V4LL1/vaccine-transport-iot/diagrams/camada analise.png

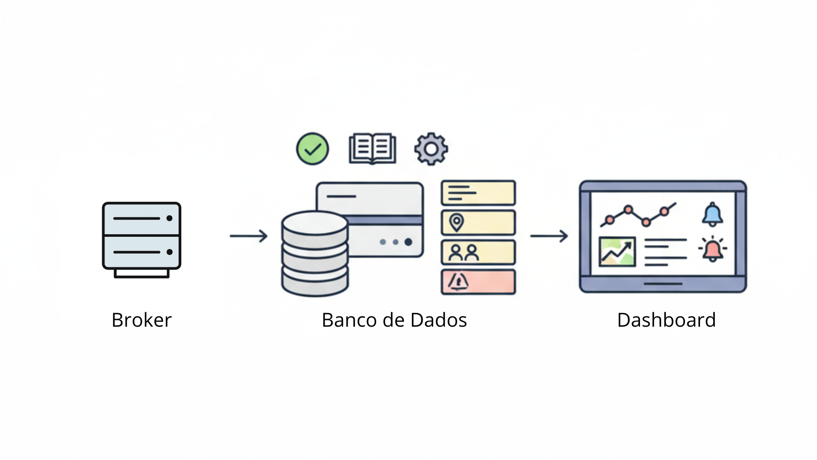
diagrams/camada analise.png
