V4LL1/vaccine-transport-iot/diagrams/camada de analise.png

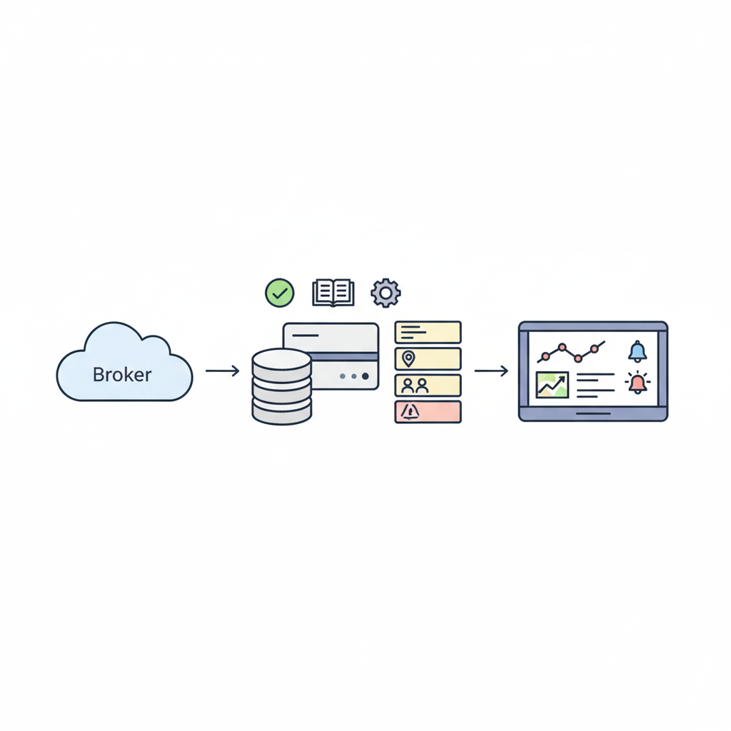
diagrams/camada de analise.png
