V4LL1/vaccine-transport-iot/diagrams/camada de ação.png

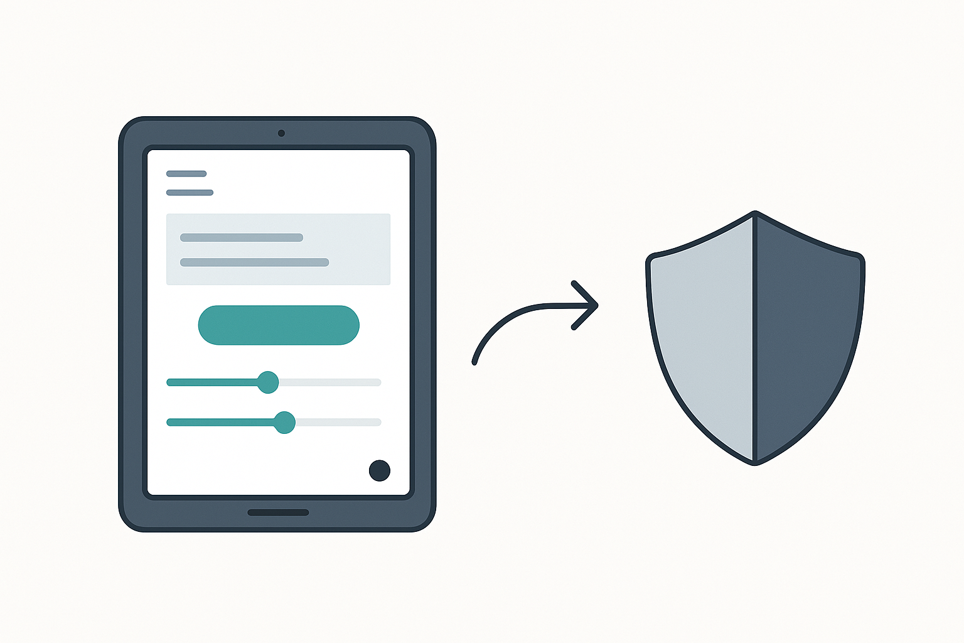
diagrams/camada de ação.png
