V4LL1/vaccine-transport-iot/diagrams/Camada de percepção (1).png

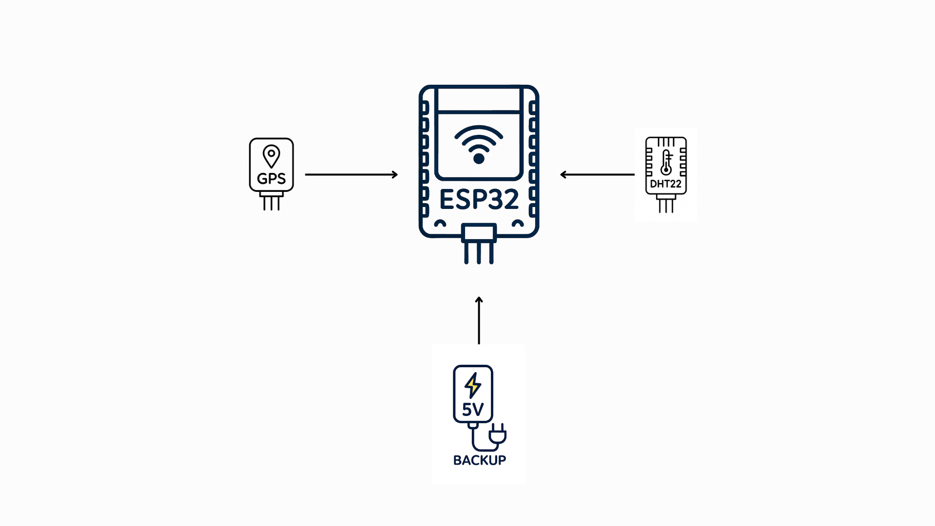
diagrams/Camada de percepção (1).png
