V4LL1/vaccine-transport-iot/diagrams/caminha com vacina.png

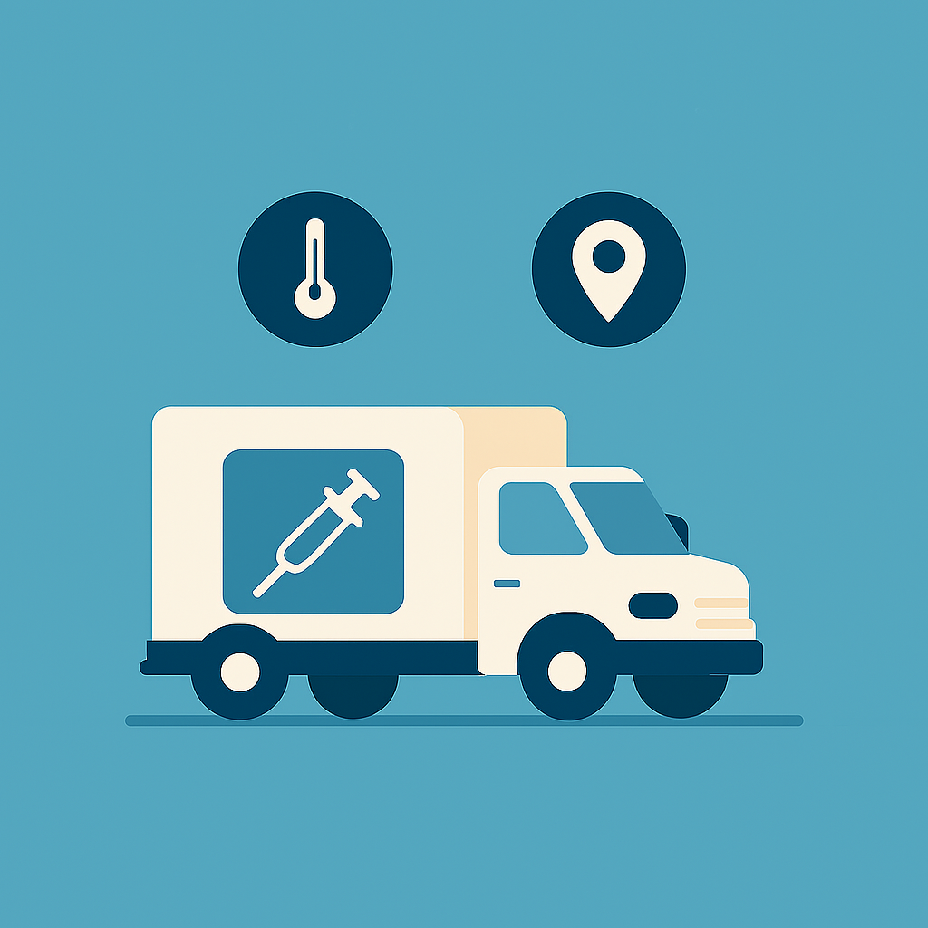
diagrams/caminha com vacina.png
