V4LL1/vaccine-transport-iot/diagrams/caminhao com vacina & hacker.png

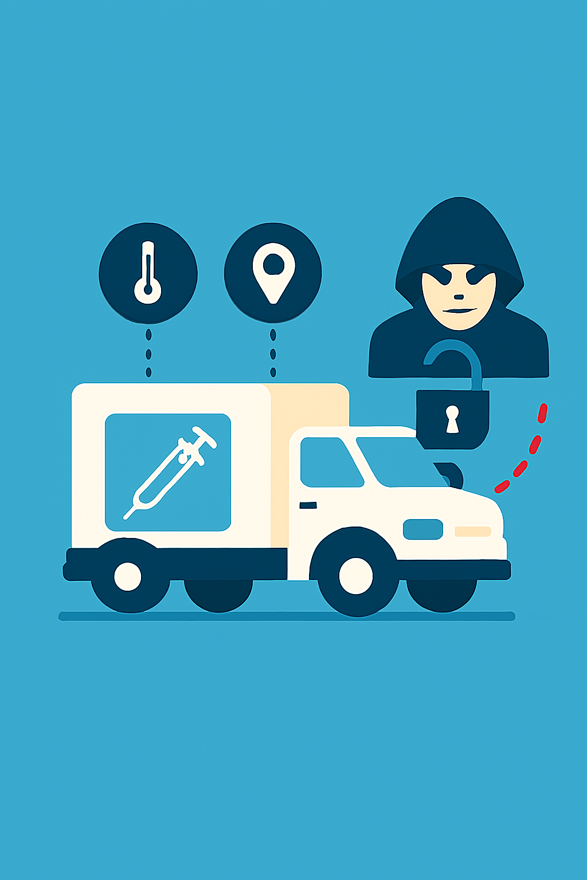
diagrams/caminhao com vacina & hacker.png
