V4LL1/vaccine-transport-iot/diagrams/database.png

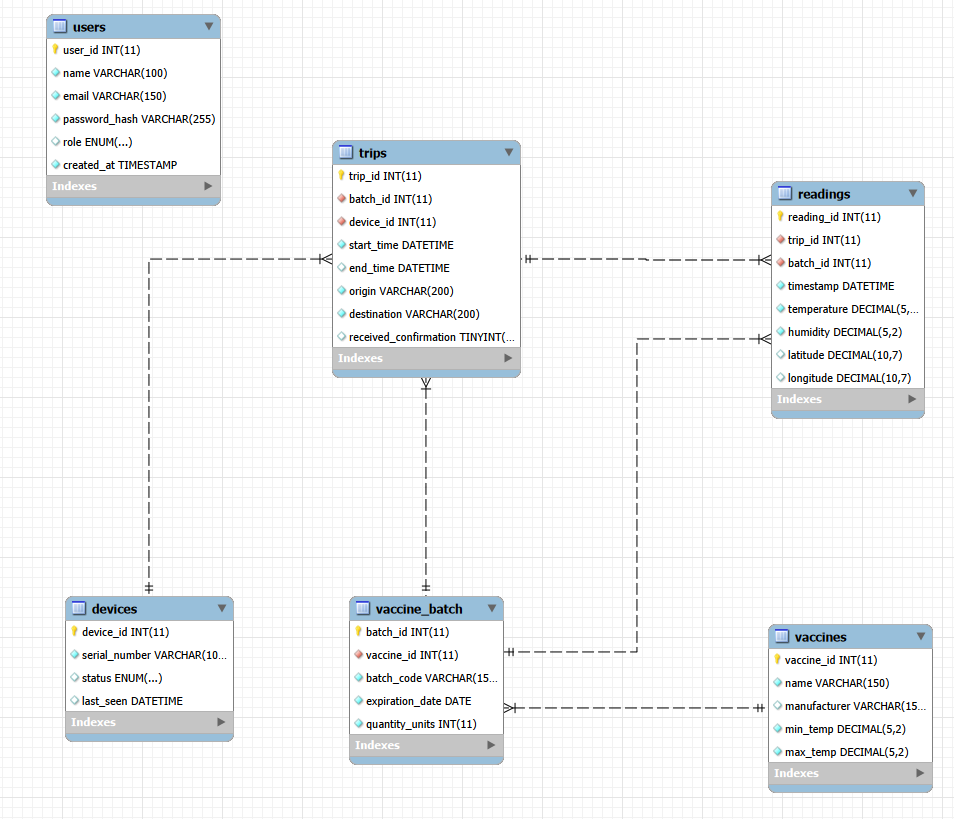
diagrams/database.png
