V4LL1/vaccine-transport-iot/diagrams/diagrama simples.png

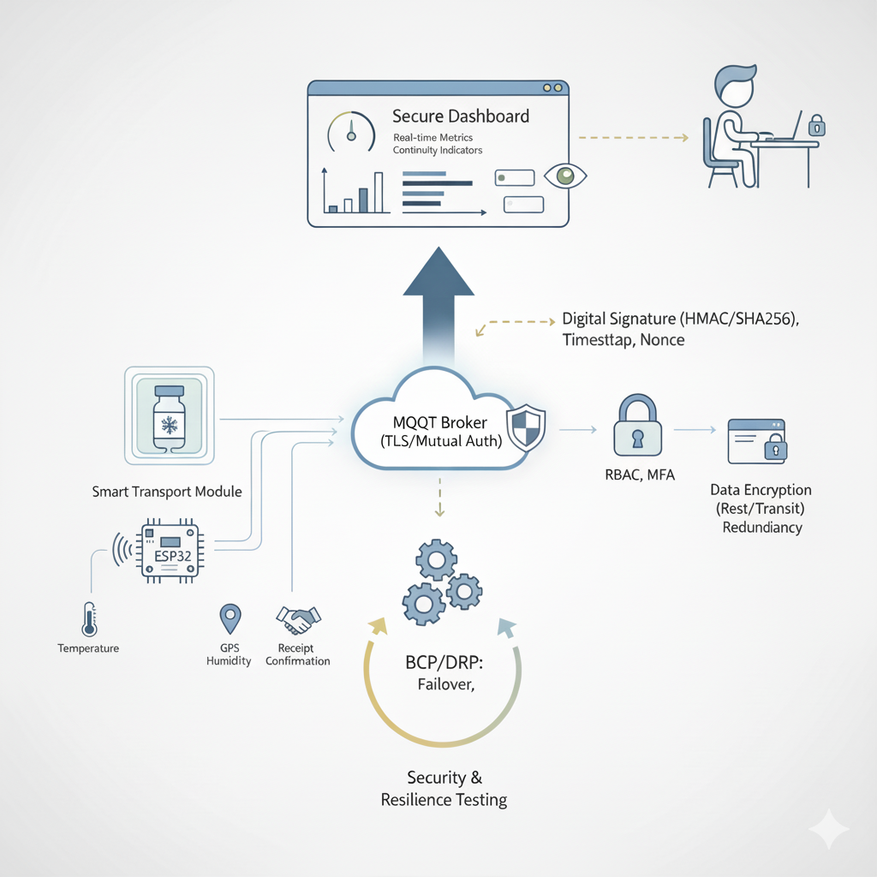
diagrams/diagrama simples.png
