V4LL1/vaccine-transport-iot/diagrams/ER.png

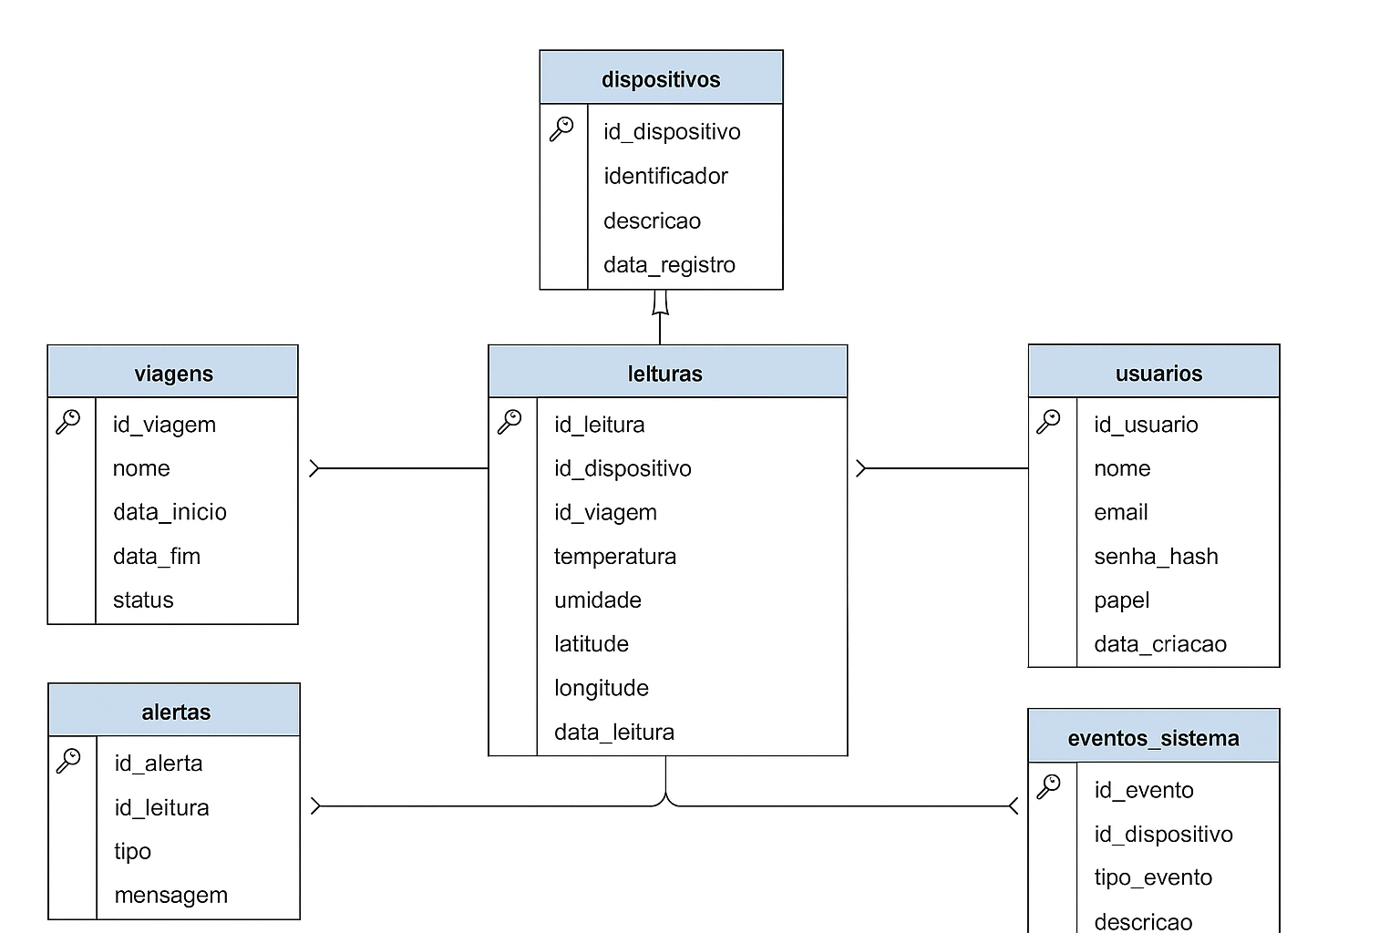
diagrams/ER.png
