V4LL1/vaccine-transport-iot/diagrams/Fases da metodologia.png

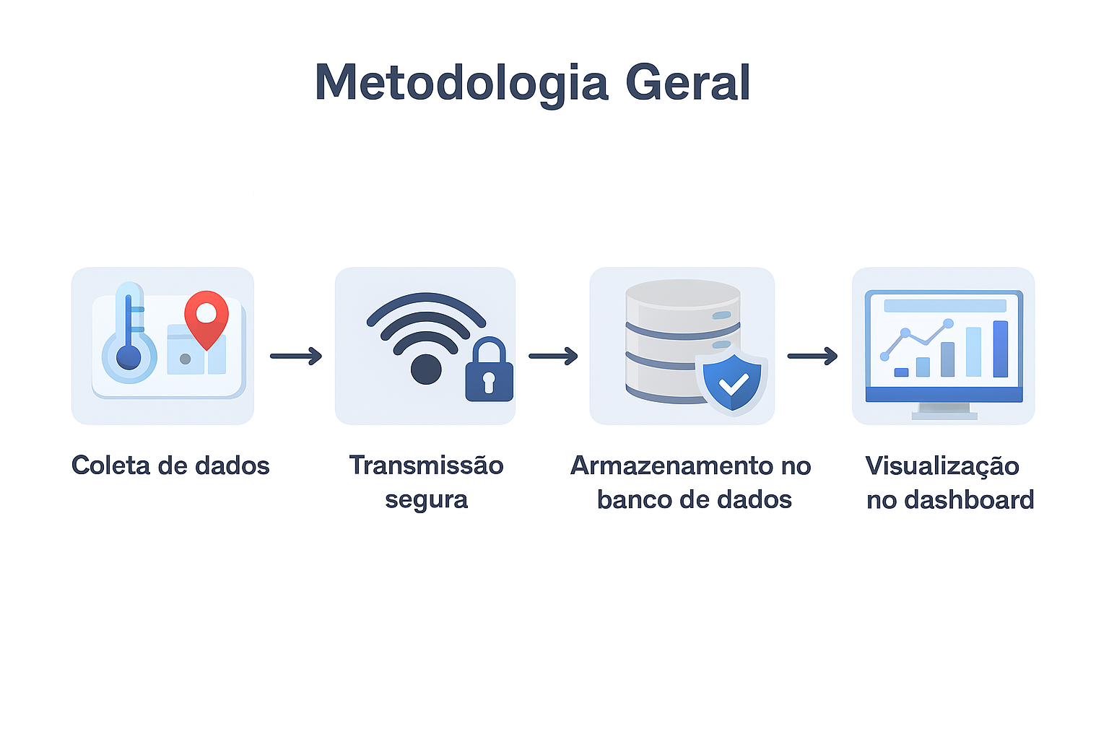
diagrams/Fases da metodologia.png
