V4LL1/vaccine-transport-iot/diagrams/individual modules/banco de dados.png

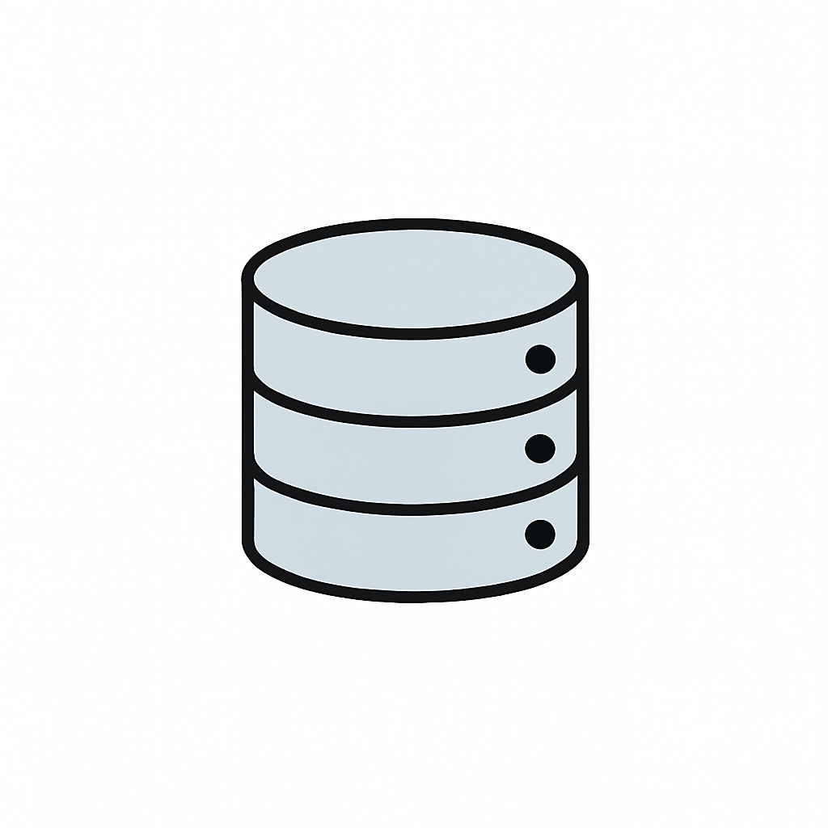
diagrams/individual modules/banco de dados.png
