V4LL1/vaccine-transport-iot/diagrams/individual modules/broker mqtt.png

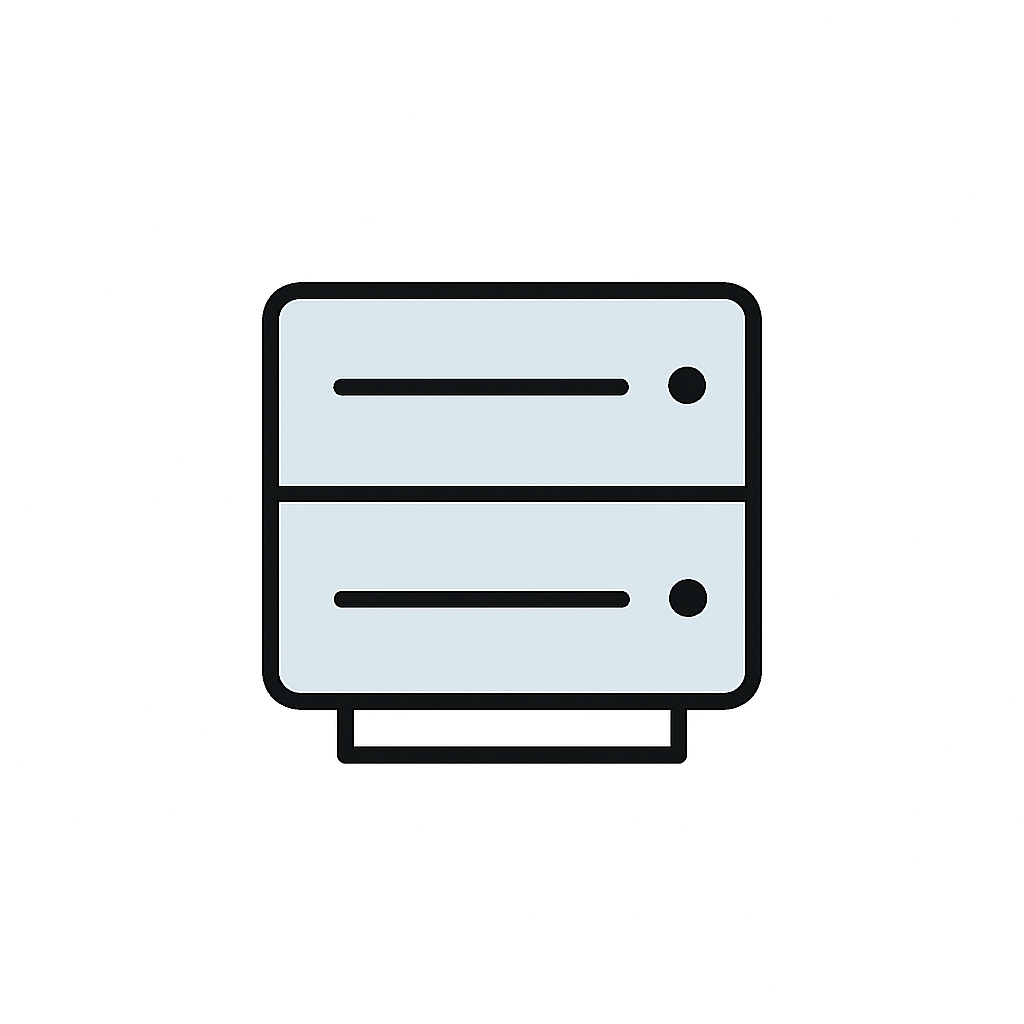
diagrams/individual modules/broker mqtt.png
