V4LL1/vaccine-transport-iot/diagrams/individual modules/cadeado.png

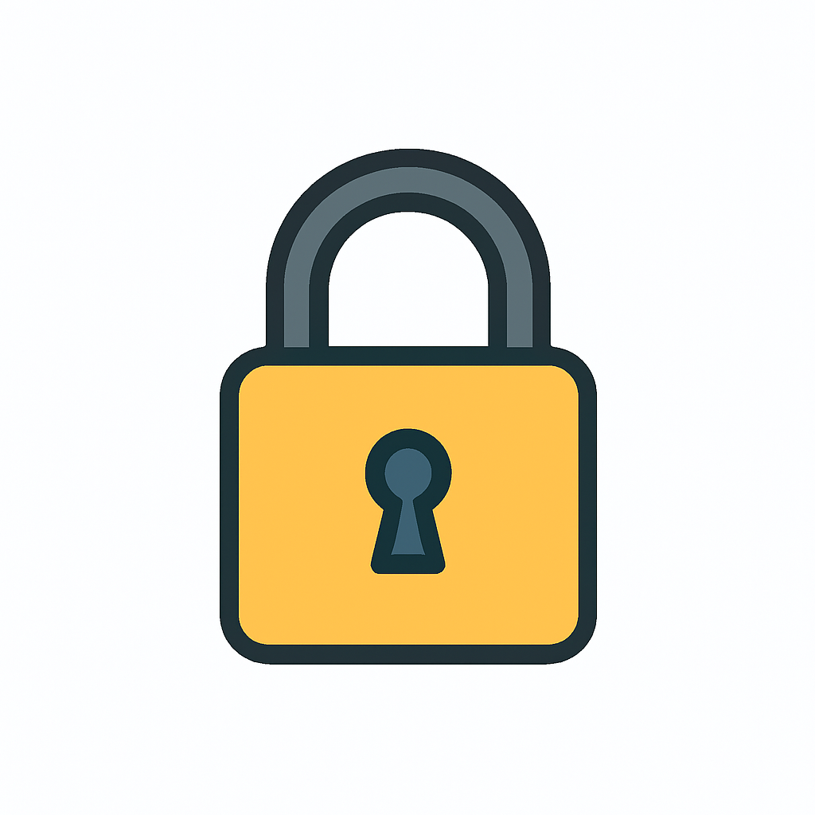
diagrams/individual modules/cadeado.png
