V4LL1/vaccine-transport-iot/diagrams/individual modules/dht22.png

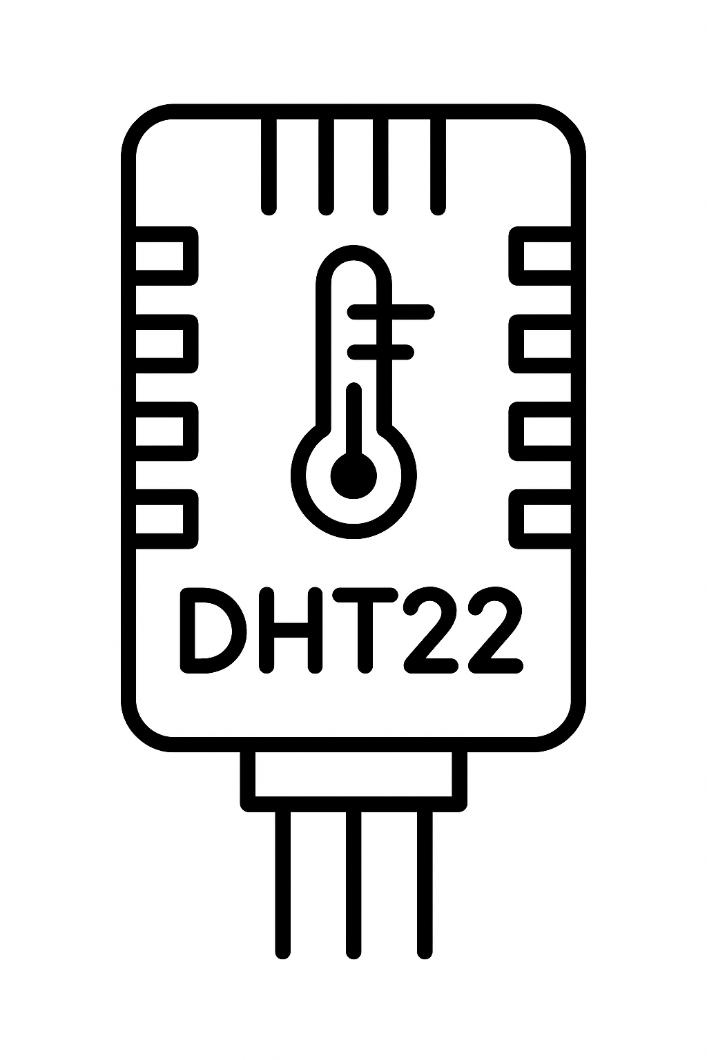
diagrams/individual modules/dht22.png
