V4LL1/vaccine-transport-iot/diagrams/individual modules/esp32.png

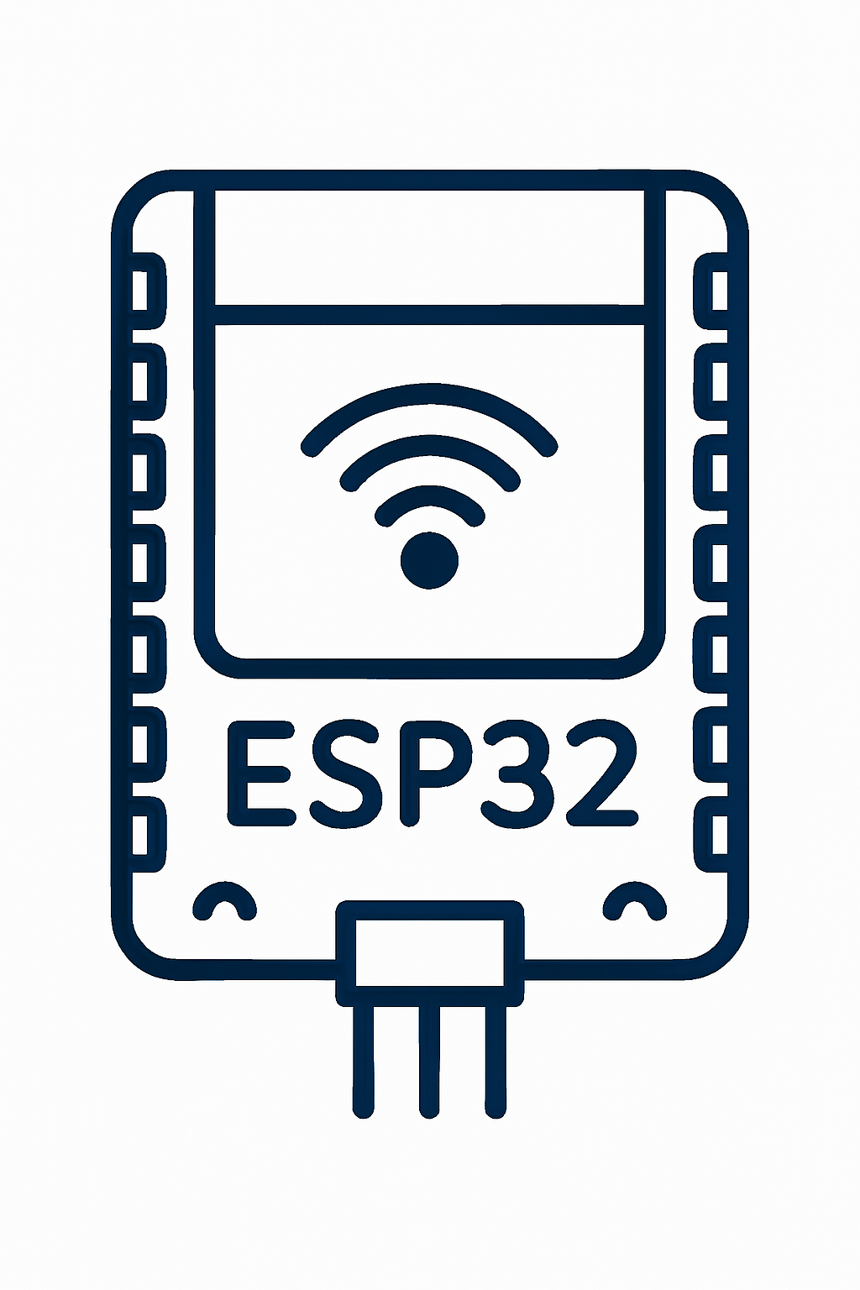
diagrams/individual modules/esp32.png
