V4LL1/vaccine-transport-iot/diagrams/individual modules/fonte.png

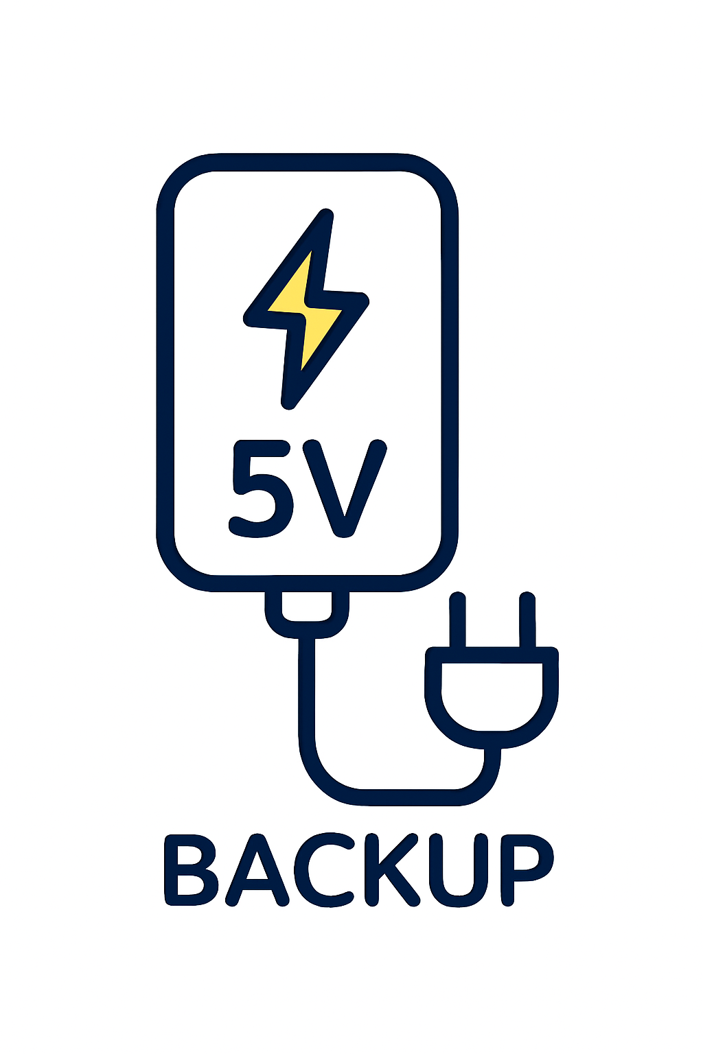
diagrams/individual modules/fonte.png
