V4LL1/vaccine-transport-iot/diagrams/individual modules/gps.png

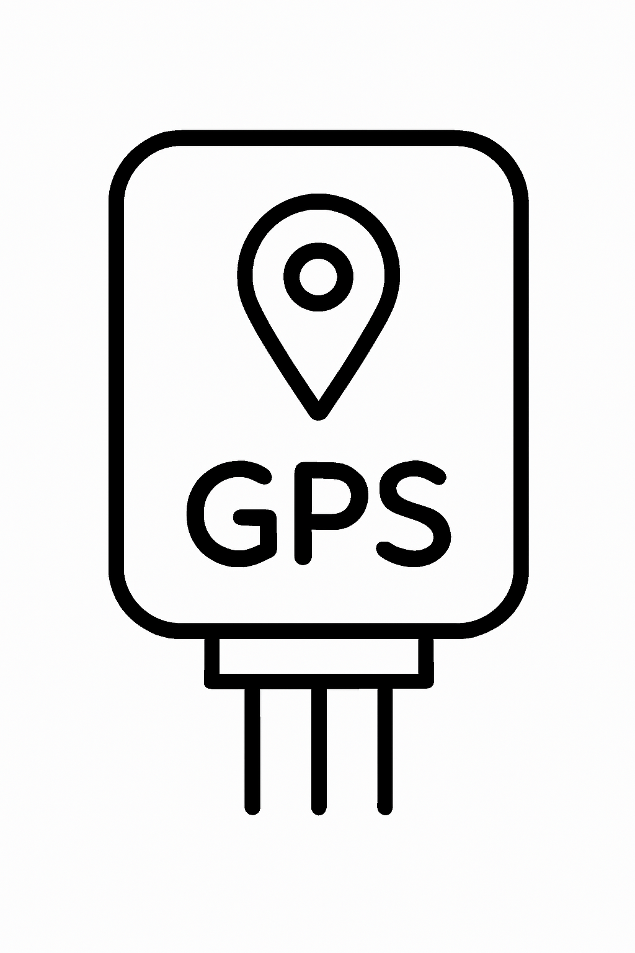
diagrams/individual modules/gps.png
