V4LL1/vaccine-transport-iot/diagrams/phisical diagram.jpg

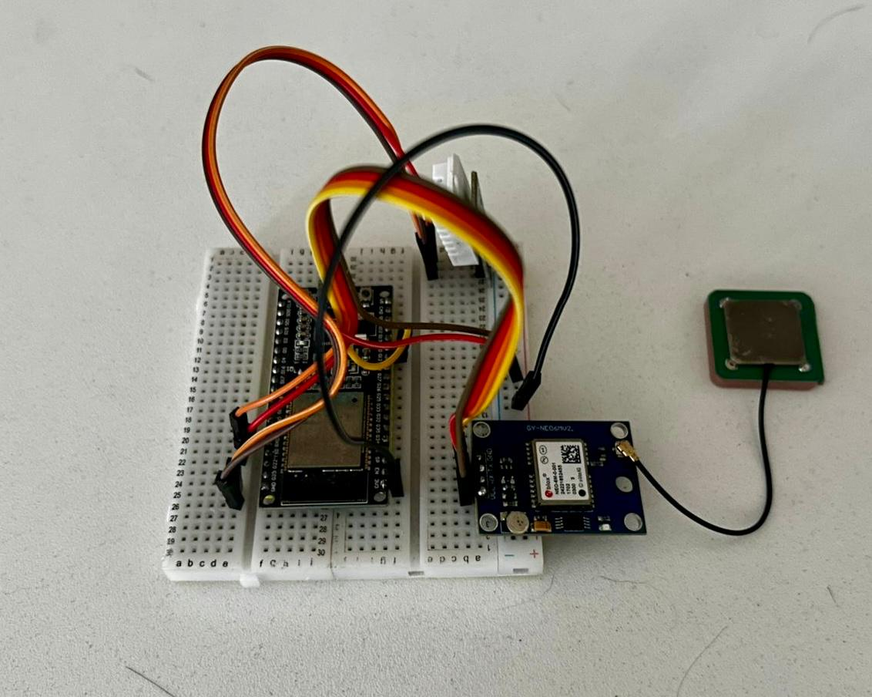
diagrams/phisical diagram.jpg
