V4LL1/vaccine-transport-iot/diagrams/sistema geral 2.png

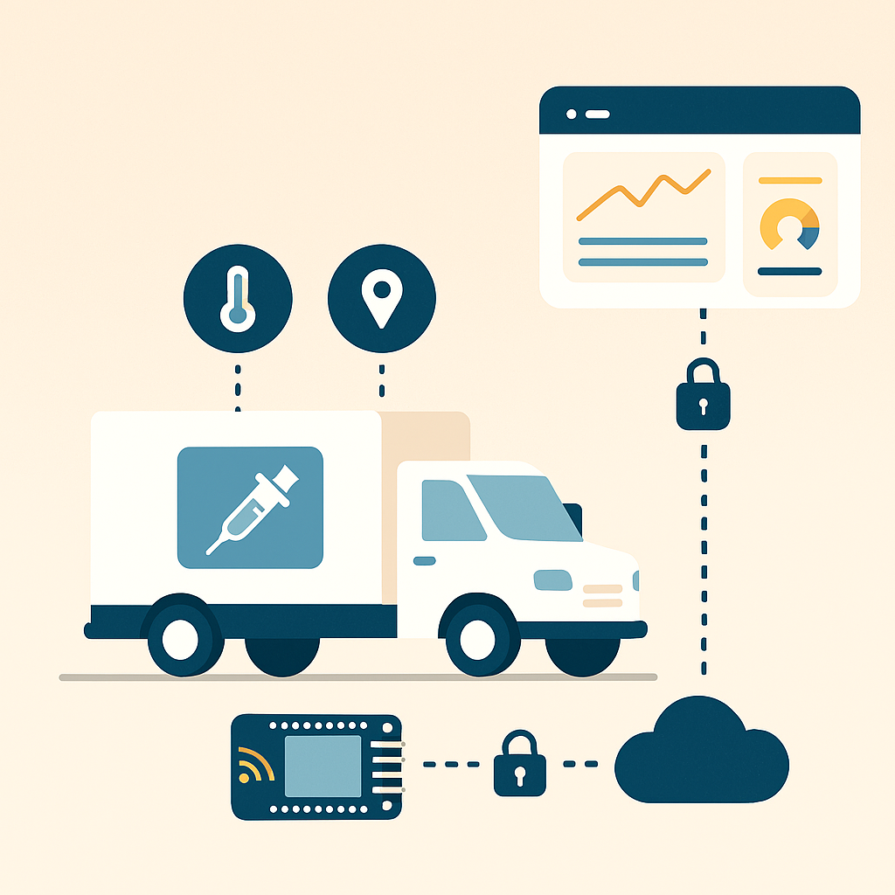
diagrams/sistema geral 2.png
