V4LL1/vaccine-transport-iot/diagrams/TG2/imagems/arduino ide.png

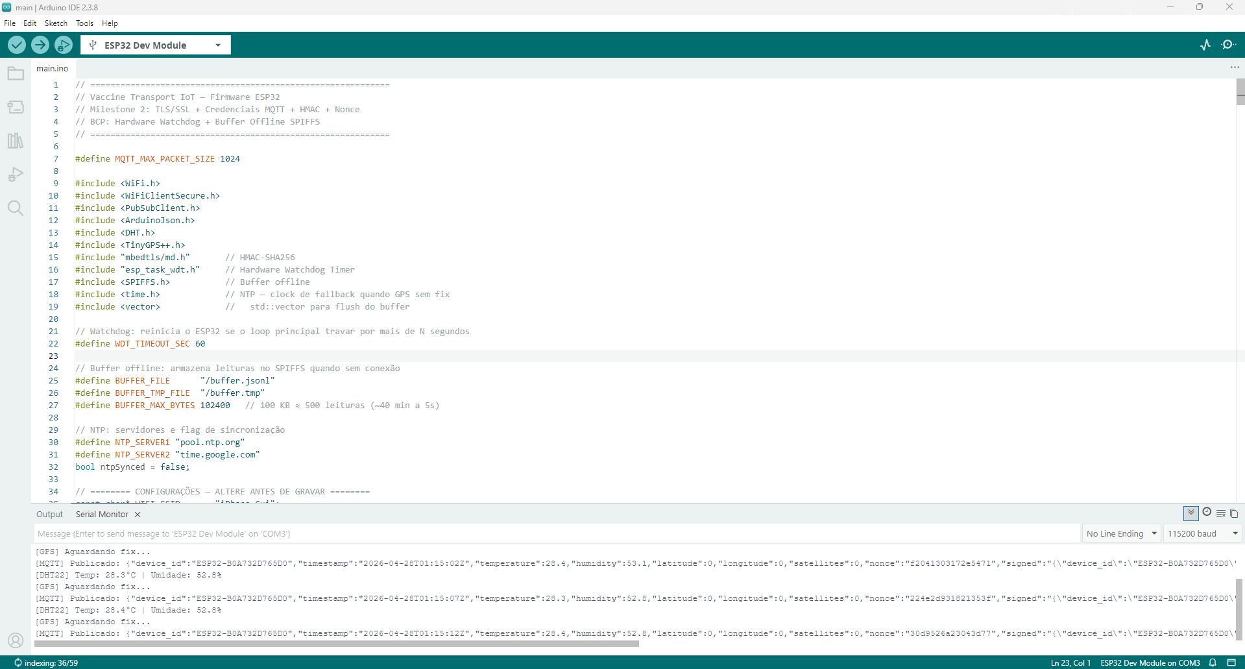
diagrams/TG2/imagems/arduino ide.png
