V4LL1/vaccine-transport-iot/diagrams/TG2/imagems/compontes .jpeg

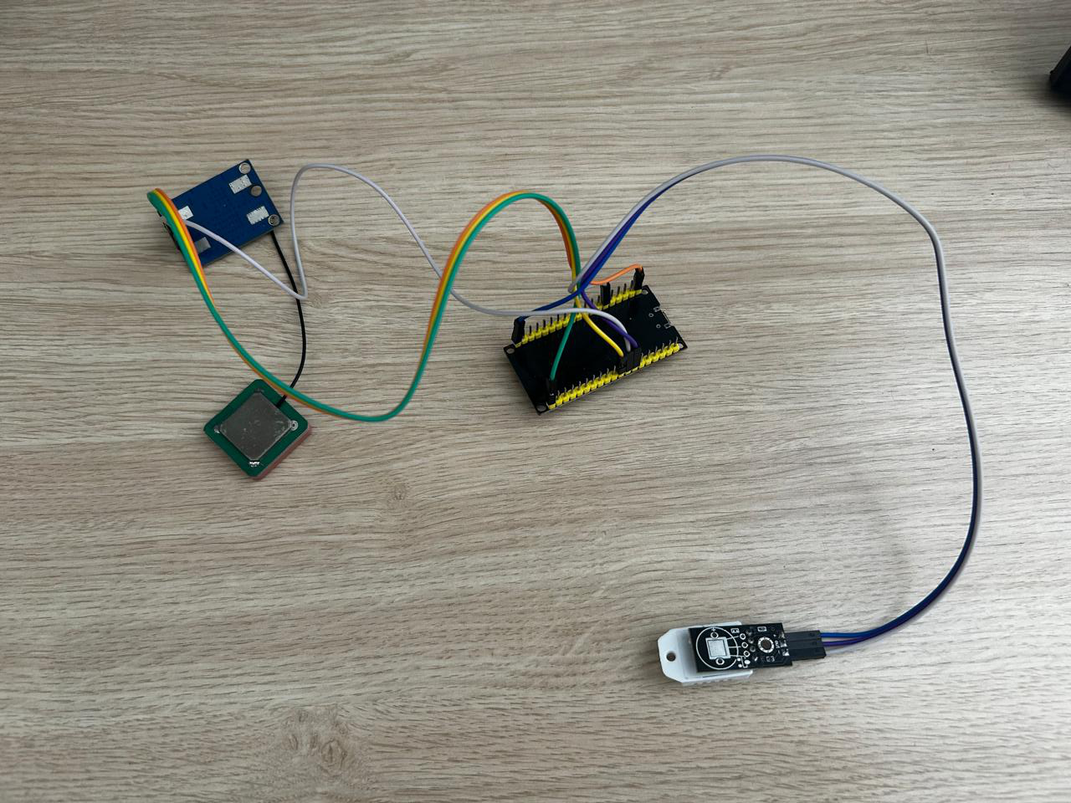
diagrams/TG2/imagems/compontes .jpeg
