V4LL1/vaccine-transport-iot/diagrams/TG2/imagems/Copilot_figura1 .png

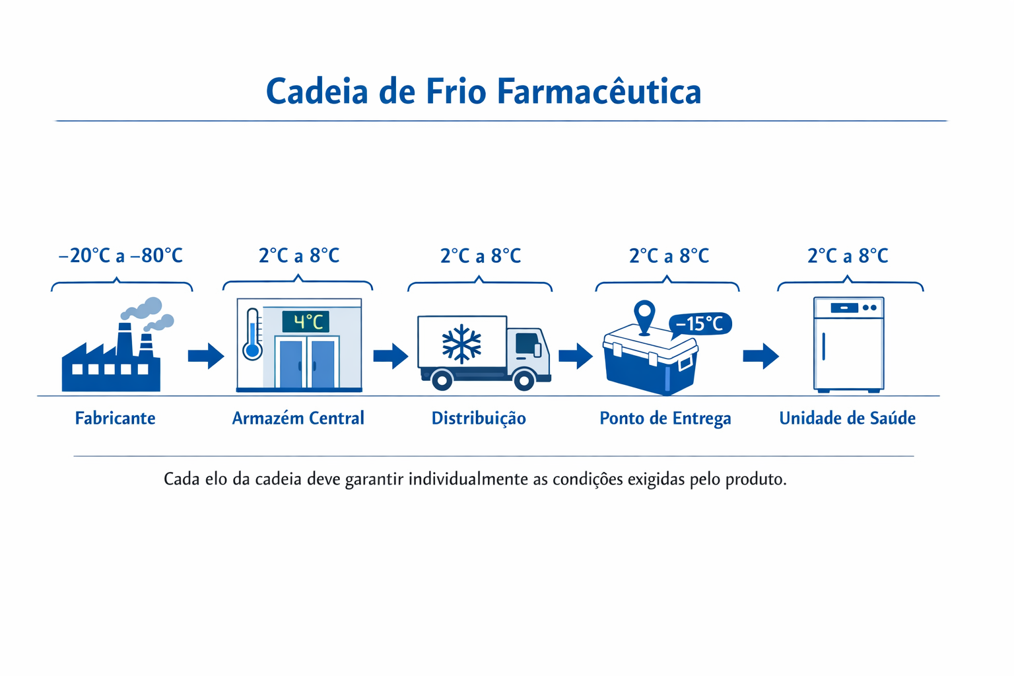
diagrams/TG2/imagems/Copilot_figura1 .png
