V4LL1/vaccine-transport-iot/diagrams/TG2/imagems/custo.png

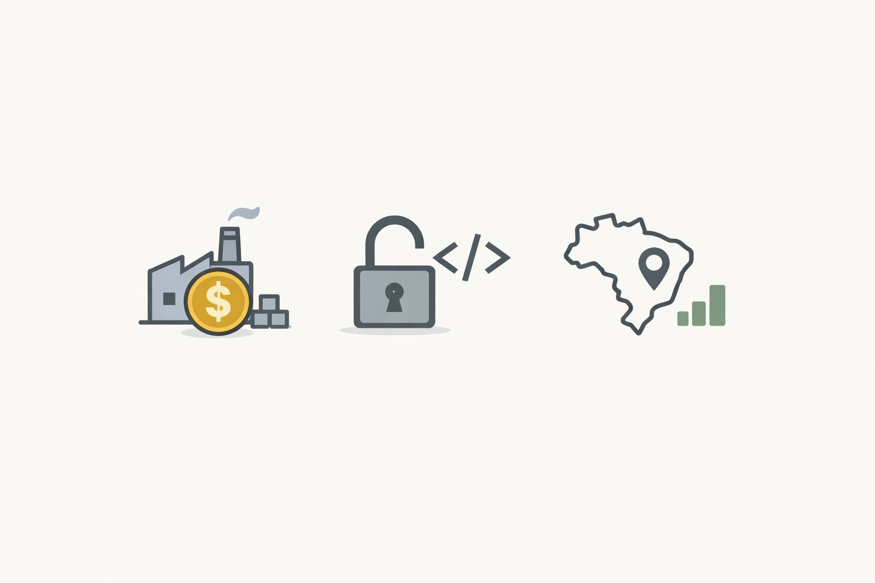
diagrams/TG2/imagems/custo.png
