V4LL1/vaccine-transport-iot/diagrams/TG2/imagems/Gemini_figura 1.png

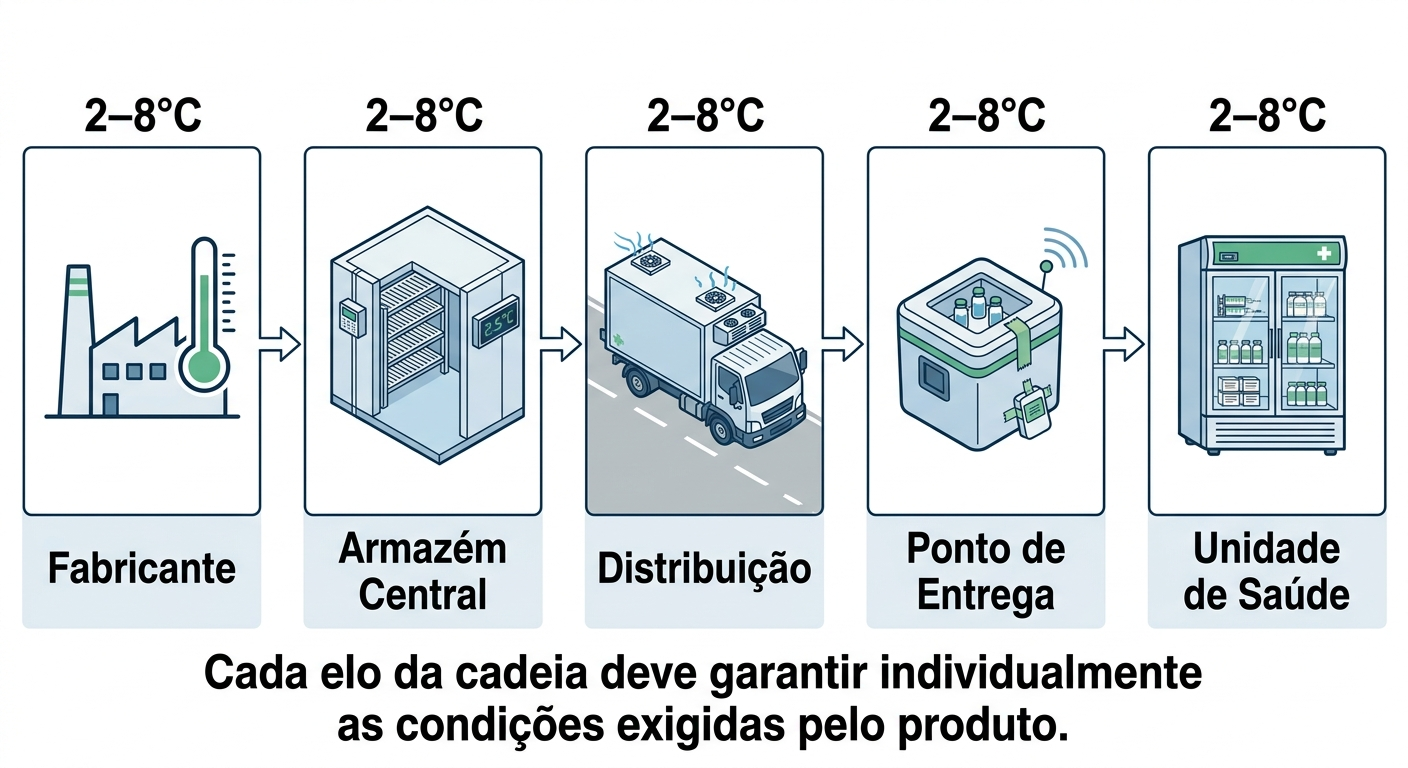
diagrams/TG2/imagems/Gemini_figura 1.png
