V4LL1/vaccine-transport-iot/diagrams/TG2/imagems/Gemini_Figura 2.png

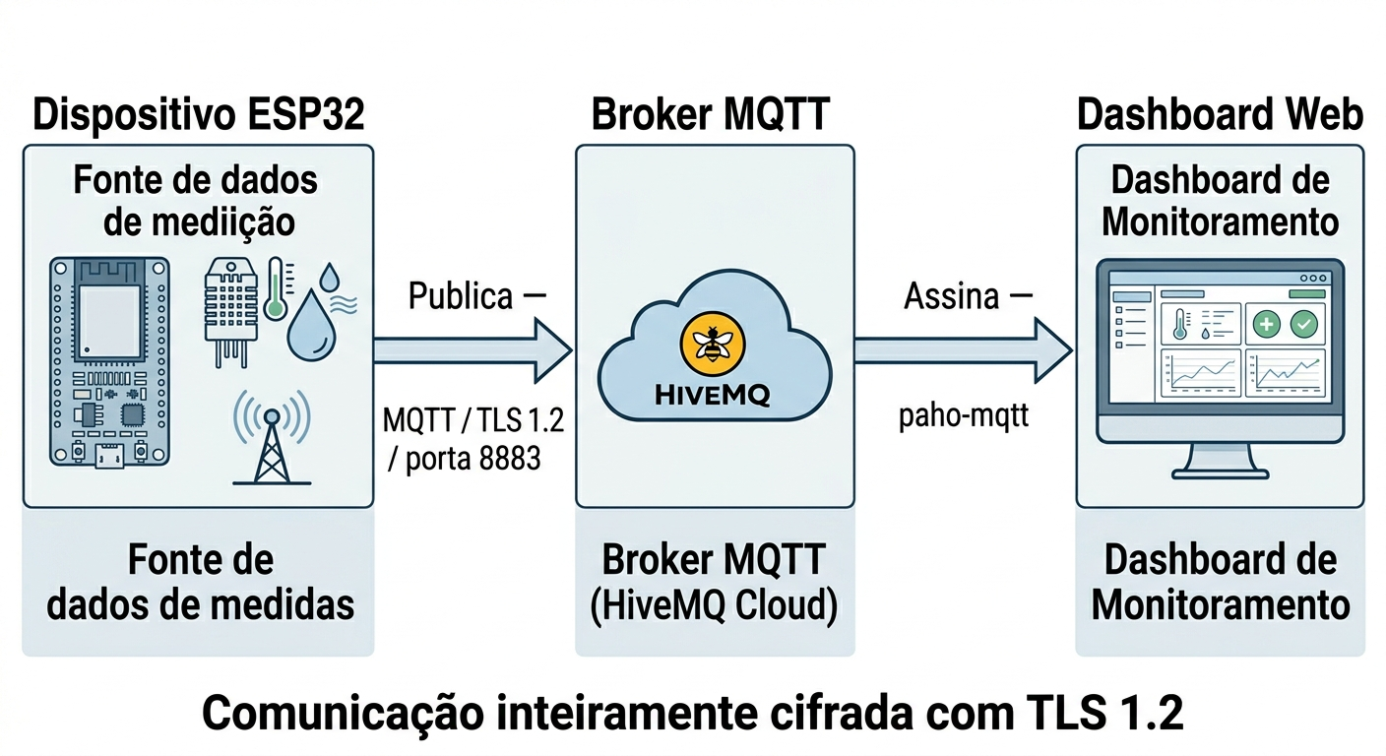
diagrams/TG2/imagems/Gemini_Figura 2.png
