V4LL1/vaccine-transport-iot/diagrams/TG2/imagems/hivemq.png

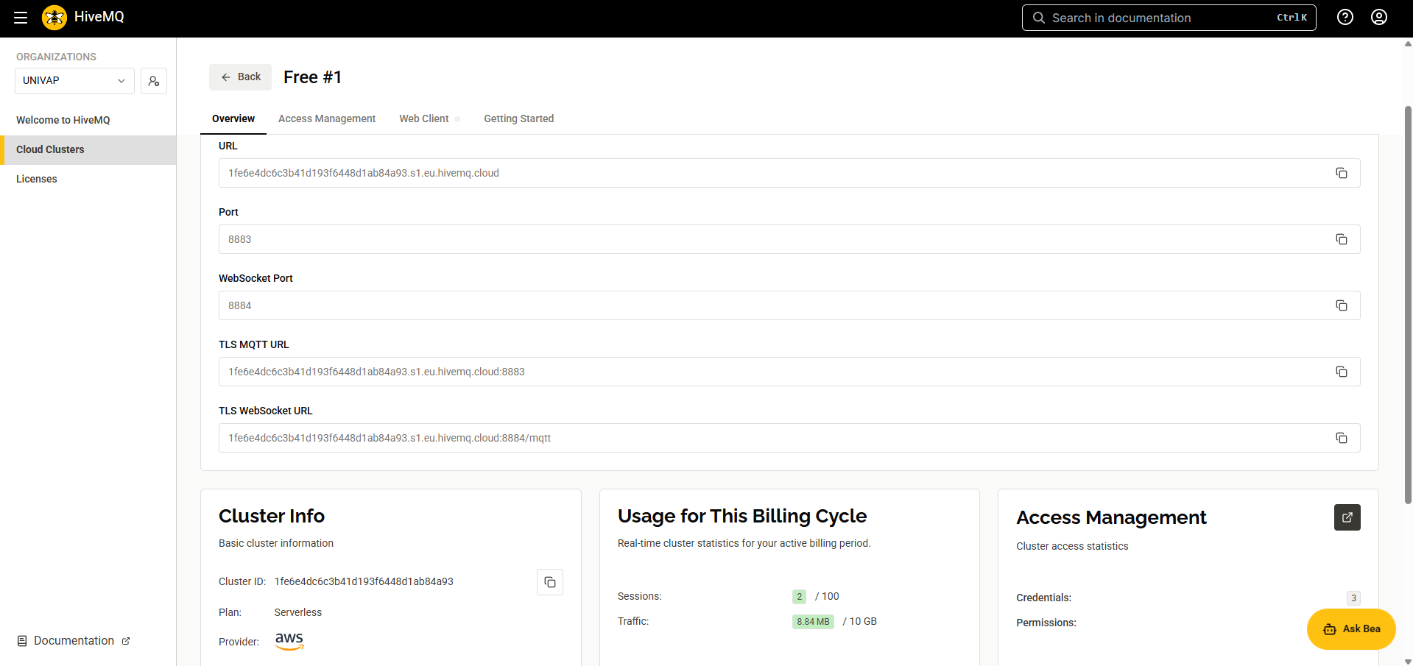
diagrams/TG2/imagems/hivemq.png
