V4LL1/vaccine-transport-iot/diagrams/TG2/imagems/tela de login.png

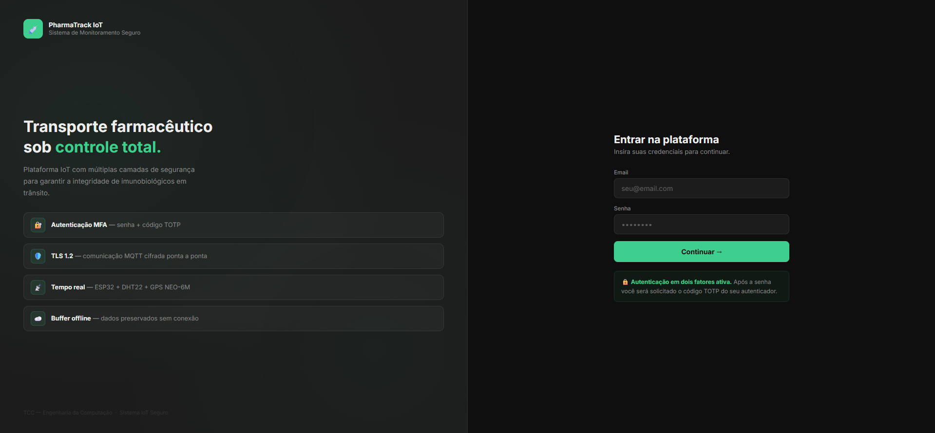
diagrams/TG2/imagems/tela de login.png
