V4LL1/vaccine-transport-iot/diagrams/TG2/imagems/tela inicial .png

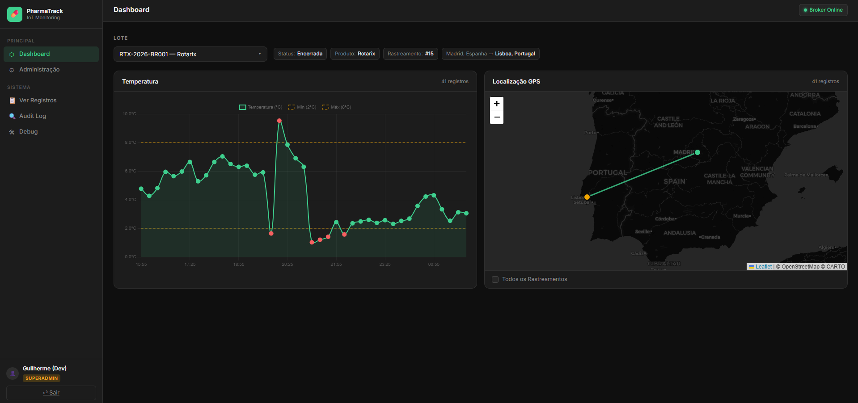
diagrams/TG2/imagems/tela inicial .png
